onuroztas1/EE463_Project_Onur_Halis_Halid/Figures/Voltage_Current_on_diode.png

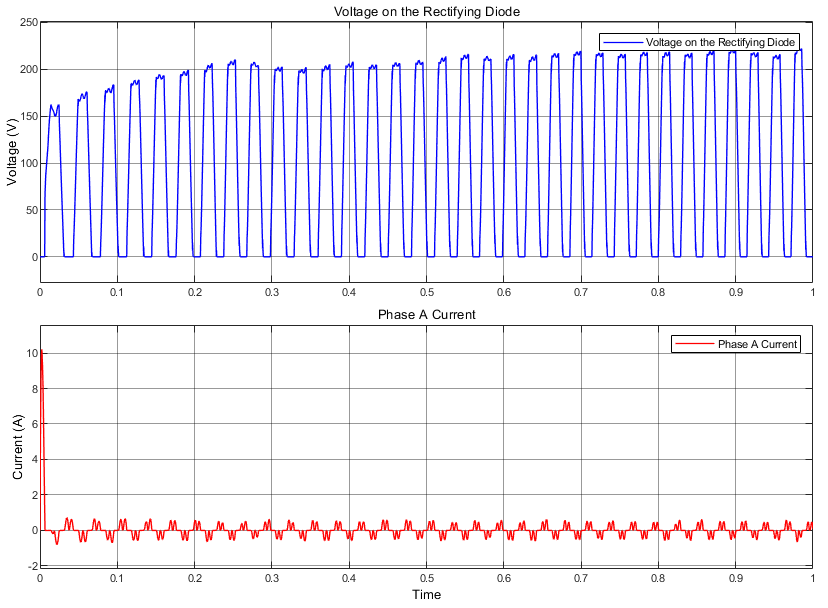
Figures/Voltage_Current_on_diode.png
