onuroztas1/EE463_Project_Onur_Halis_Halid/Figures/Voltage_of_fwd.png

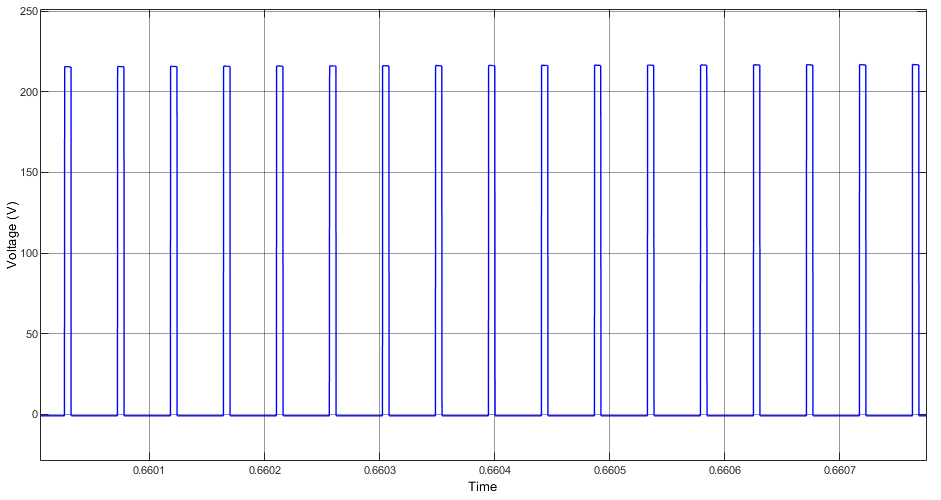
Figures/Voltage_of_fwd.png
