onuroztas1/EE463_Project_Onur_Halis_Halid/PCB_Kicad/main/3d_view3.png

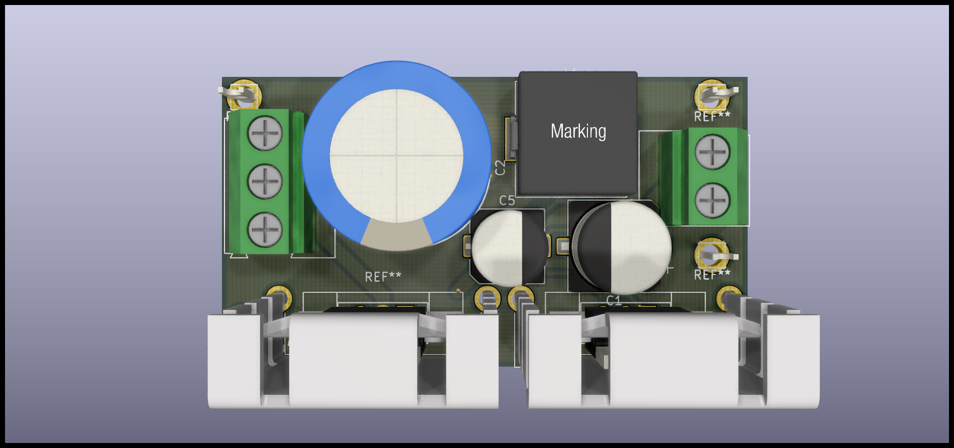
PCB_Kicad/main/3d_view3.png
