onuroztas1/EE463_Project_Onur_Halis_Halid/PCB_Kicad/main/step_files/LTC3854EMSEPBF.step

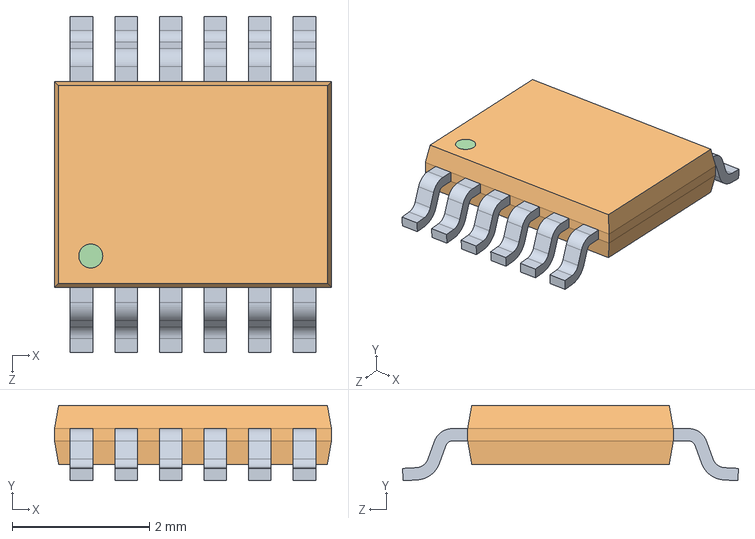
[picture p28: CAD file, 2021-01-01]
PCB_Kicad/main/step_files/LTC3854EMSEPBF.step
4.04 x 1.10 x 4.90 mm
