onuroztas1/EE463_Project_Onur_Halis_Halid/PCB_Kicad/main/step_files/sk_129_25.4_sts.stp

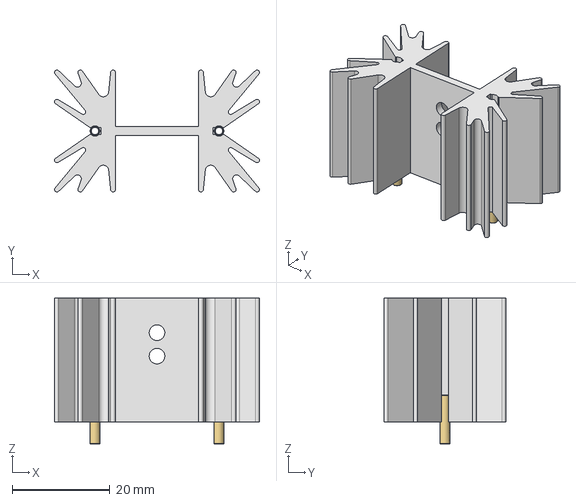
[picture p29: CAD file, 2020-12-24]
PCB_Kicad/main/step_files/sk_129_25.4_sts.stp
42.0 x 25.0 x 29.9 mm
A9001B20100008S x 2
