onuroztas1/EE463_Project_Onur_Halis_Halid/Heat_Anlysis/main-Thermal 2/main-Thermal 2-Results-Thermal1.analysis.png

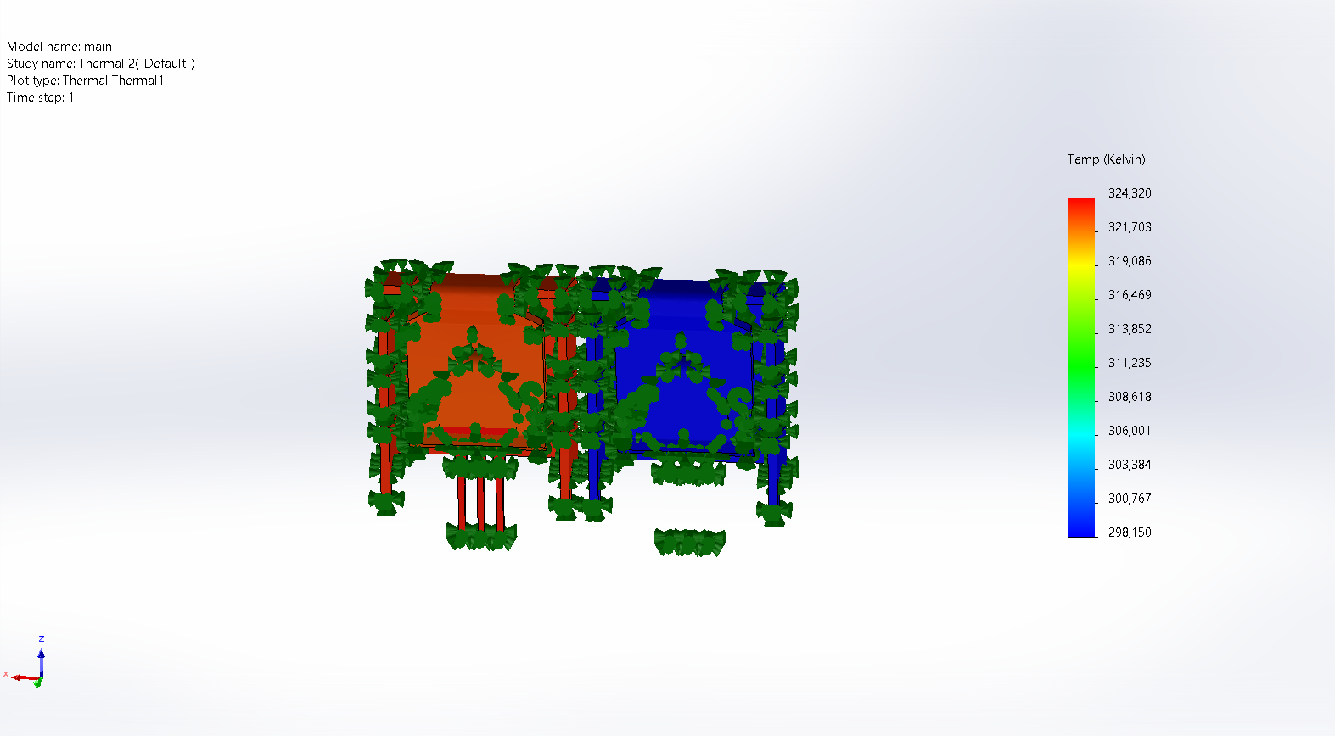
Heat_Anlysis/main-Thermal 2/main-Thermal 2-Results-Thermal1.analysis.png
