onuroztas1/EE463_Project_Onur_Halis_Halid/PCB_Kicad/main/back.pdf

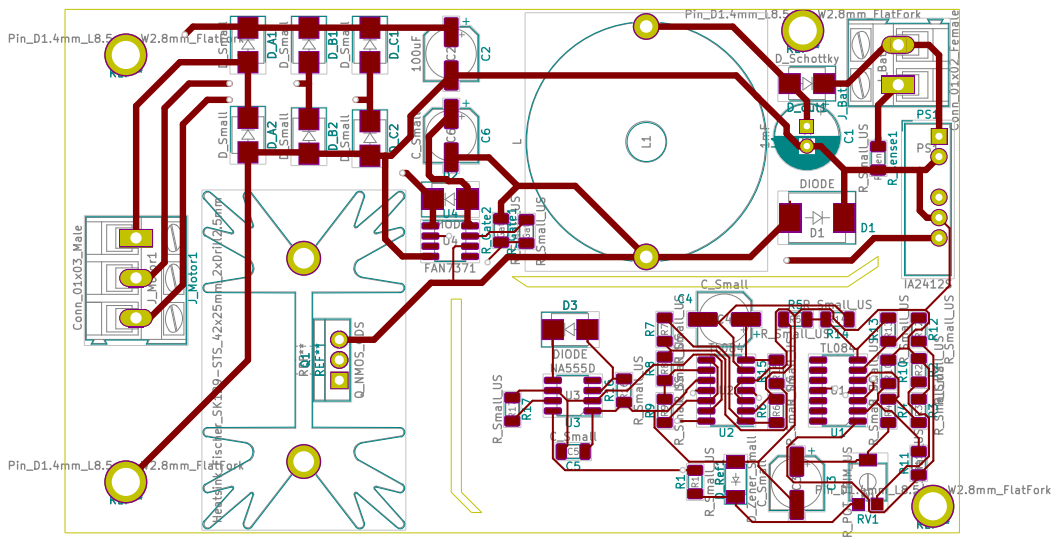
[picture p31: page 1]
