onuroztas1/EE463_Project_Onur_Halis_Halid/PCB_Kicad/main/circuit.pdf

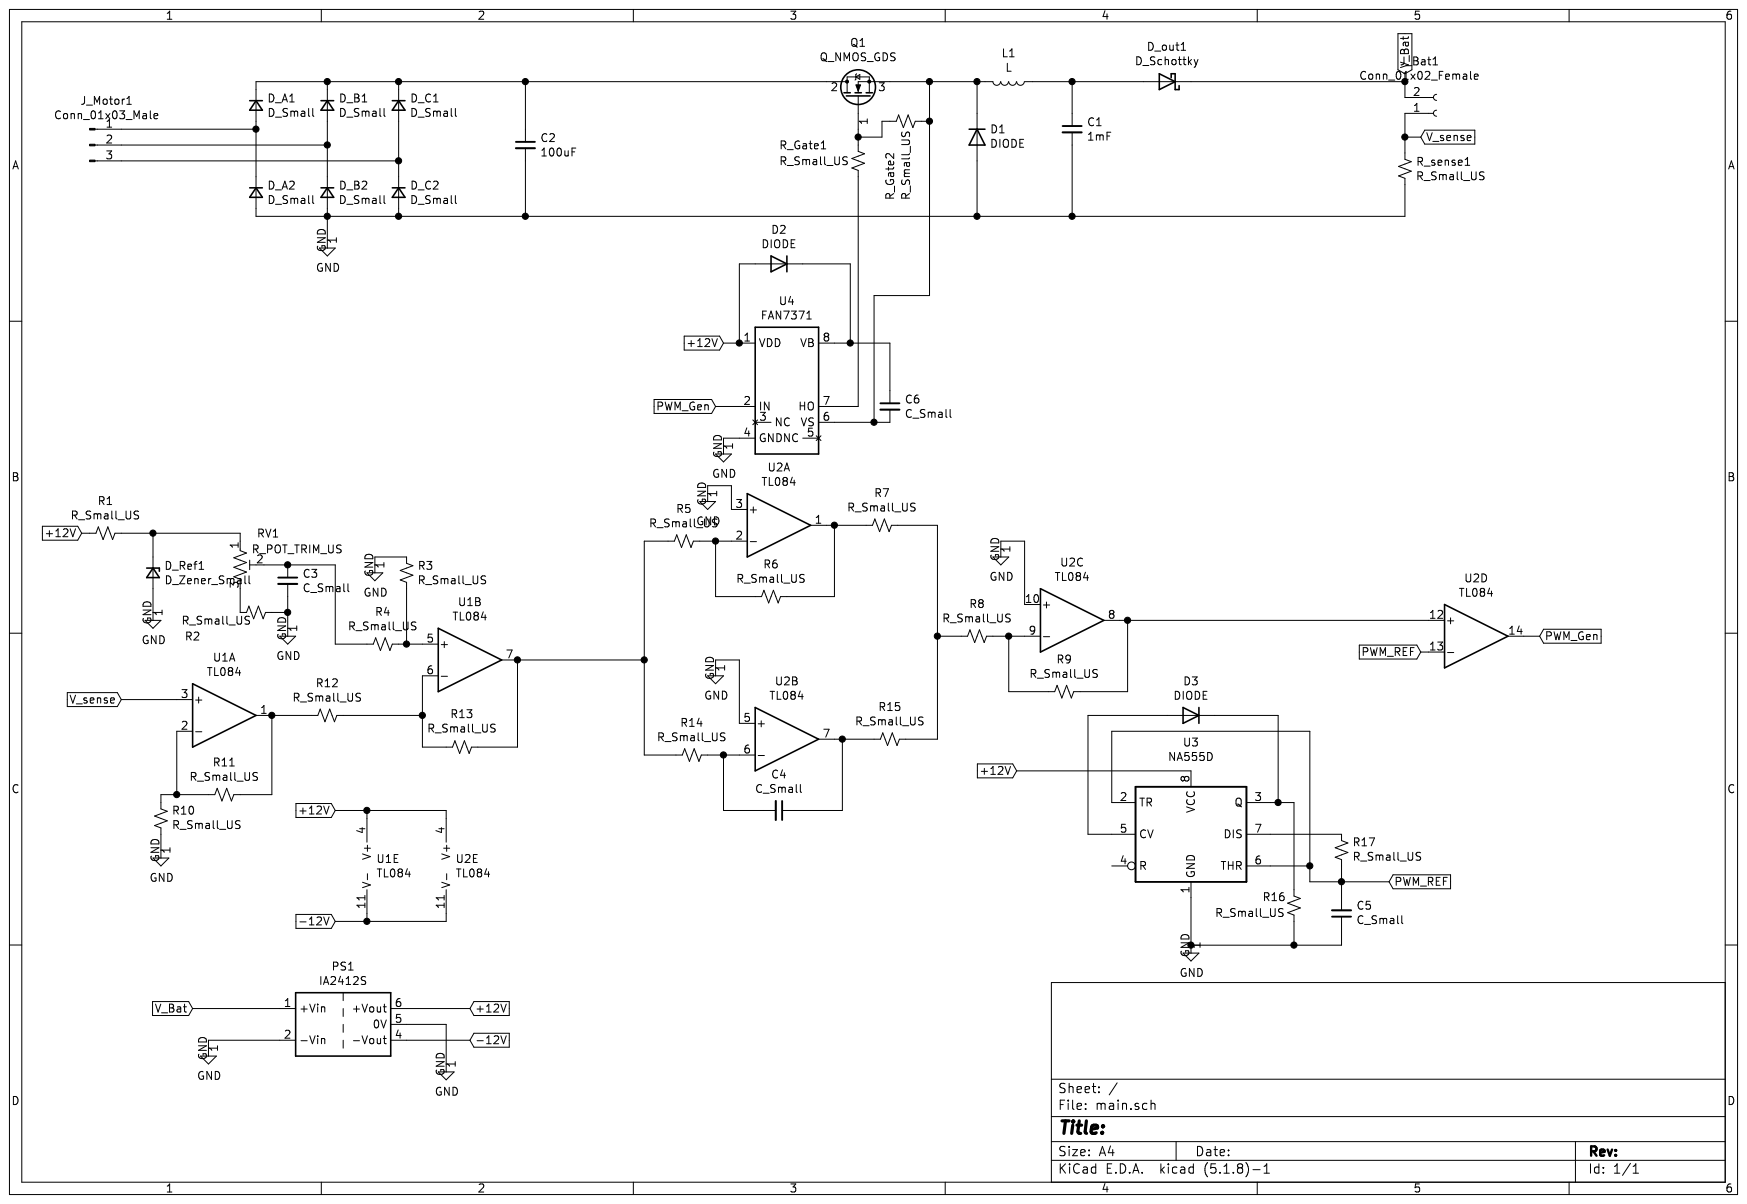
[picture p32: page 1]
