onuroztas1/EE463_Project_Onur_Halis_Halid/PCB_Kicad/main/front.pdf

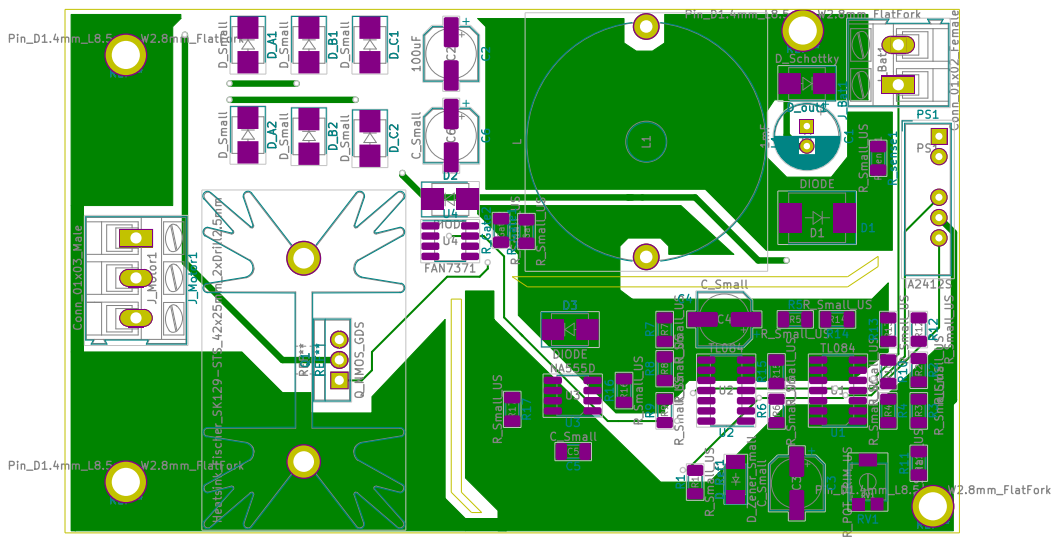
[picture p33: page 1]
