onuroztas1/EE463_Project_Onur_Halis_Halid/Buck_test.asc

C1: cap; 10000mF; IC=24
C2: cap; 470µ
C6: cap; 1µ
D1: diode; RFN5BM3S
D2: diode; RFUH20NS3S
L1: ind; 100µ
Q1: nmos; R6020PNJ
Q2: nmos; R6020PNJ
R14: res; 0.1
U3: ir2104_
V1: voltage; 300
V2: voltage; 12
V3: voltage; PULSE(0 5 0 10n 10n 2.15u 25u)
Named nets: Vin, 0, Vcc
.tran 0 1 10m startup uic
.options gmin=1e-10
.options abstol=1e-10
.options reltol=0.003
.options cshunt=1e-15
