onuroztas1/EE463_Project_Onur_Halis_Halid/ltspice_test.asc

C1: cap; 100nF
C2: cap; 470µ
C3: cap; 10000mF; IC=24
D1: schottky; MBR745
D2: diode; RRE02VS4S
I1: current; 2
L1: ind; 100µh
R1: res; 2.7k
R2: res; 0.1
R3: res; 100k
R4: res; 0.1
R5: res; 10k
R7: res; 2.21k
R10: res; 12
U1: LT1074HV
U2: LT1006
V1: voltage; 50
V2: voltage; 24v
V3: voltage; -24v
Named nets: 0, v+, v-
.tran 100m uic
.temp 25
.options gmin=1e-10
.options abstol=1e-5
.options reltol=0.003
.options cshunt=1e-15
