onuroztas1/EE463_Project_Onur_Halis_Halid/LTspice simulation.asc

ACS70331EESATR-2P5B3: e; 4
Bat: res; 0.1
C1: cap; 680µF; Rser=4.5m
C2: cap; 4.7µ
C3: cap; 2.2n
C4: cap; 8000m; IC=24
C5: cap; 2200p; Rser=15K Cpar=100p
C6: cap; 1µ
C7: cap; 4.7µ
C8: cap; 4.7µ
C9: cap; 10µ
D1: diode; RF01VM2S
L1: ind; 100µ; Rser=140m
Q1: nmos; IPP200N25N3
Q2: nmos; IPP200N25N3
R3: res; 0.1
R4: res; 1k5
U1: LTC3854
V1: voltage; 24
V2: voltage; SINE(250 100 30)
Named nets: 0, IN, Vin
.tran 0 30m 0 startup
