onuroztas1/EE463_Project_Onur_Halis_Halid/3854.asc

ACS70331EESATR-2P5B3: e; 4
C1: cap; 680µF; Rser=4.5m
C2: cap; 4.7µ
C3: cap; .0002µ
C4: cap; 8000m; IC=24
C5: cap; 2200p; Rser=15K Cpar=100p
C6: cap; 1µ
C7: cap; 10µ
C8: cap; 10n
D1: diode; RF01VM2S
L1: ind; 100µ; Rser=140m
Q1: nmos; IPP200N25N3
Q2: nmos; IPP200N25N3
R1: res; 0.1
R3: res; 0.1
U1: LTC3854
V1: voltage; 24
V2: voltage; SINE(250 50 30)
Named nets: 0, IN
.tran 0 100m 0 startup
