onuroztas1/EE463_Project_Onur_Halis_Halid/TL494.asc

C1: cap; 10n
C2: cap; 1m
C3: cap; 100n
C5: cap; 10000mF; IC=24
C6: cap; 1µ
D1: schottky; 1N5819
D2: diode; RFUH20NS3S
L1: ind; 100µ
Q1: nmos; IXFX90N30
Q2: nmos; IXFX90N30
R1: res; 10k
R2: res; 1k
R3: res; 560
R4: res; 2k2
R5: res; 3.3k
R6: res; 330
R7: res; 50k
R8: res; 0.1
R9: res; 10k
R10: res; 10k
R11: res; 470
R12: res; 10k
R13: res; 0.11
R14: res; 100
R15: res; 10k
R16: res; 1k
R17: res; 10k
R18: res; 10k
U1: TL494
U2: UniversalOpamp2
U3: ir2104_
U5: INV_1
V1: voltage; 300
V2: voltage; 12
V3: VOLTAGE; 12; Rser=0.02
V4: VOLTAGE; -12; Rser=0.02
Named nets: 0, Vin, Vcc, V_ADJ, Vref, Imax, Ilim
.tran 0 1 10m startup uic
.options gmin=1e-10
.options abstol=1e-5
.options reltol=0.003
.options cshunt=1e-15
