onuroztas1/EE463_Project_Onur_Halis_Halid/Draft1.asc

C1: cap
C2: cap; 470µ
D1: diode
L1: ind; 100µ
M1: nmos
R1: res; 10
R2: res; 100
U1: IR2117
V1: voltage; 400
V2: voltage; 24
V3: voltage; PULSE(0 5 0 10n 10n 10u 20u)
Named nets: 0
