onuroztas1/EE463_Project_Onur_Halis_Halid/Draft2.asc

C1: cap; 470µ
D1: schottky; MBRB2545CT
L1: ind; 100µ
M1: nmos; R6020PNJ
R1: res; 12
V1: voltage; 400
V2: voltage; PULSE(0 4 0 1p 1p 10u 20u)
Named nets: 0
