onuroztas1/EE463_Project_Onur_Halis_Halid/GATE_driver.asc

C1: cap; 100p
C2: cap; 0.1µ
C3: cap; 10µ
R1: res; 10
R2: res; 10k
R3: res; 2.2
R4: res; 49.9k; tol=1
R5: res; 12.4k; tol=1
R6: res; 84.5k; tol=1
R7: res; 330k
U1: LTC4441
V1: voltage; PULSE(0 20 0 0.00000001 0.00000001 0.01 0.02)
V2: voltage; 24
Named nets: 0
.tran 0 0.1 0
