onuroztas1/EE463_Project_Onur_Halis_Halid/PI_PWM_circuit.asc

C1: cap; 10µ; Rser=1u
C2: cap; 1n; Rser=1u
D1: diode
R1: res; 5k
R2: res; 5k
R3: res; 5k
R4: res; 5k
R5: res; 1k
R6: res; 10k
R7: res; 5k
R8: res; 1k
R9: res; 3k
R10: res; 5k
R11: res; 68k
R12: res; 2.2k
R13: res; 1k
U1: UniversalOpamp2
U2: UniversalOpamp2
U3: UniversalOpamp2
U4: UniversalOpamp2
U5: UniversalOpamp2
U6: NE555
V1: voltage; 2
V2: voltage; 12
V3: voltage; SINE(2 5 250)
V4: voltage; 12
V5: voltage; -12
Named nets: 0, IL, -Vcc, +Vcc, pwm
.tran 0 0.1 0 0.001
