onuroztas1/EE463_Project_Onur_Halis_Halid/LT1074_TA01.asc

C1: POLCAP; 230µ; Rser=0.05
C2: POLCAP; 500µ; Rser=0.07
C3: cap; .01µ
C4: cap; 10000mf; IC=24
D1: schottky; MBRS140
L1: ind; 100µ
R1: RES; 2.7k
R2: RES; 1k
R3: RES; 9.86k
R4: res; 0.1
R5: res; 10k
R6: res; 1k
Rload: res; 0.1
U1: LT1074
U2: UniversalOpamp2
V1: VOLTAGE; SINE(50 10 300); Rser=0.02
V2: VOLTAGE; 12; Rser=0.02
V3: VOLTAGE; -12; Rser=0.02
Named nets: 0, OUT, IN
.tran 20m
LT1074 - Step-Down Switching Regulator
Input: 10V to 40V       Output: 5V @ 5A
Note:
  If the simulation model is not found please update with the "Sync Release" command from the "Tools" menu.
  It remains the customer's responsibility to verify proper and reliable operation in the actual application.
  Component substitution and printed circuit board layout may significantly affect circuit performance or reliability.
  Contact your local sales representative for assistance. This circuit is distributed to customers only for use with LTC parts.
  Copyright © 2011 Linear Technology Inc. All rights reserved.
